arthurbenemann/OPA_PHONO/Simulation/LTC3265.asc

C1: cap; 1µ
C2: cap; 1µ
C3: cap; 10µ; Rser=5m
C4: cap; 10µ; Rser=5m
C5: cap; 100n
C6: cap; 10µ; Rser=5m
C7: cap; 100n
C8: cap; 10µ; Rser=5m
R1: res; 5.1k
R2: res; 20.5k
R3: res; 5.1k
R4: res; 20.5k
Rload+: res; 250R
Rload-: res; 250R
U1: LTC3265
V1: VOLTAGE; 5V
Named nets: 0, IN, OUT+, OUT-
.tran 6m startup
