arthurbenemann/OPA_PHONO/Simulation/RIAA_Filter.asc

AC1: voltage; AC 5m
C1: cap; {mc(68n,tolc)}
C2: cap; {mc(68n,tolc)}
C3: cap; {mc(47n,tolc)}
C4: cap; 1µ
C5: cap; 1µ
C6: cap; {X}
E1: e; Laplace=(((1+3180u*s)*(1+75u*s))/((1+318u*s)))/10
L1: ind; 450m
OPA1612: opamp; Aol=1Meg
OPA1644: opamp; Aol=1Meg
R1: res; {mc(16k,tolr)}
R2: res; {mc(2.32k,tolr)}
R4: res; 16k
R5: res; 499R
R6: res; 16k
R7: res; 499R
R8: res; 47k
R9: res; 47k
R10: res; 47k
R11: res; 750
R13: res; 47k
Rbypass: res; {Rbyp}
U3: opamp
Named nets: 0, vout, vin
.ac dec 20 0.1 1Meg
;.step param run 1 50 1
.param tolr=0.01 tolc=0.02 X=102p
Laplace=(((1+3180u*s)*(1+75u*s))/((1+318u*s)*(1+3.18u*s)))/10
.lib opamp.sub
*.step param X list 50p 100p 120p
cartridge model from OM10 https://www.ortofon.com/om-series-p-550
;ac dec 20 20 20k
.meas AC RIAA_dev_pp PP V(vout)
.step param Rbyp list 1G 1f
